m6r3k/Avocado-HiFi-amplifier/LTspice/PreAMP.asc

C1: cap; 120p
C2: cap; 15n
C3: cap; 68n
C4: cap; 10µ
C5: cap; 100µ
C6: cap; 47n
C7: cap; 68n
C8: cap; 10µ
C9: cap; 100µ
C10: cap; 68n
C11: cap; 68n
C12: cap; 100n
C13: cap; 10µ
C14: cap; 100µ
C15: cap; 68n
E1: e; Laplace=(1+3180u*S)*(1+75u*S)/(1+318u*S)
R1: res; 47k
R2: res; 2k
R3: res; 100R
R4: res; 27k
R5: res; 3k3
R6: res; 4k7
R7: res; 220R
R8: res; 2k
R9: res; 2k
R10: res; 100R
R11: res; 16k
R12: res; 4k7
R13: res; 4k7
R14: res; 220R
R15: res; 2k
R16: res; 2k
R17: res; 100R
R18: res; 22k
R19: res; 3k18
R20: res; 4k7
R21: res; 220R
R22: res; 2k
R23: res; 4k7
U1: LT1115
U2: LT1115
U3: LT1115
U4: LT1115
U5: LT1115
U6: LT1115
V1: voltage; 12V
V2: voltage; 12V
V3: voltage; SINE(); AC 4m
Named nets: -12V, +12V, 0, AntiRIAA, Output1, Output2, Output3, IN
.ac oct 1000 10 30000
PhonoBox - 2012
RIAA filter Muffsy
RIAA filter m6r3k
